micccy/scoreboard/pcb/mic5677_displaydriver/front.pdf

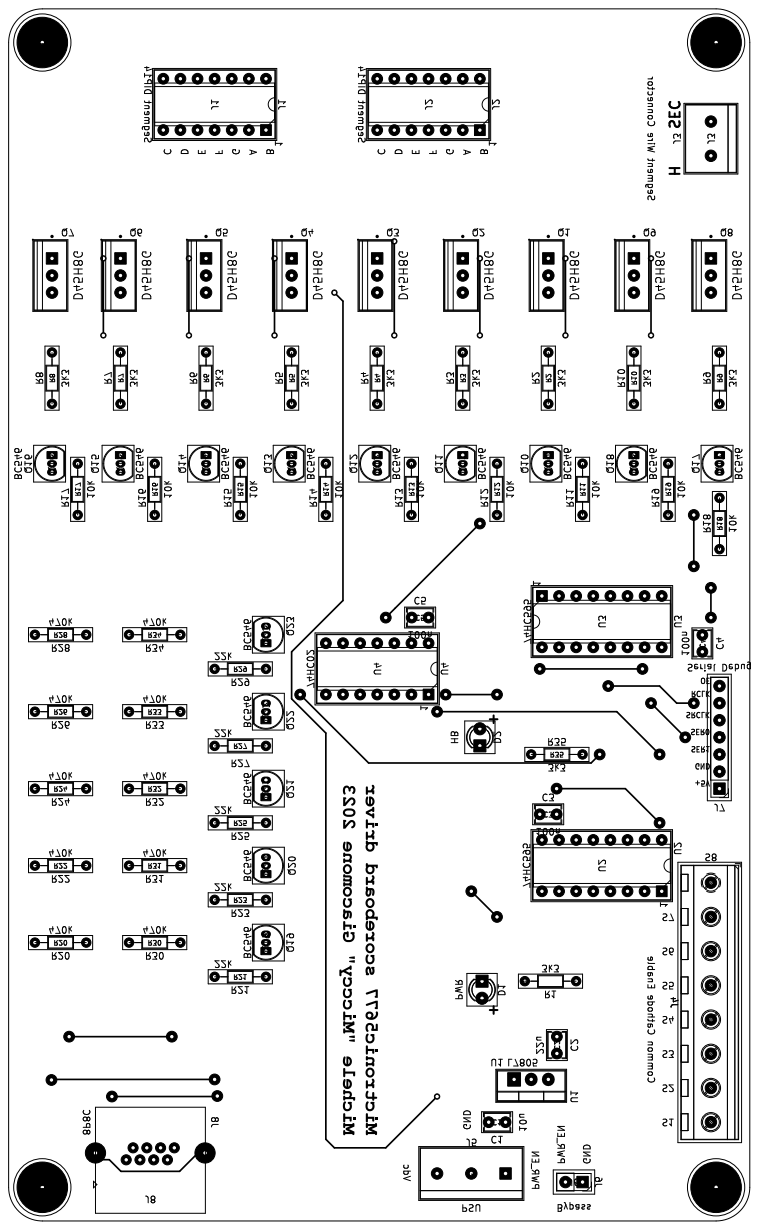
[picture p5: page 1]

H +5V GND + S6 GND B S5 GF SEC

Michele "Micccy" Giacomone 2023 S4S2 E SRCLK SER1 C OE 1 1 CEFDG 1 S8 S1S3 A SER0 GND S7 PWR_EN 1 PWR_EN RCLK DA + B 1 Q11
