micccy/scoreboard/pcb/mic5677_displaydriver/back.pdf

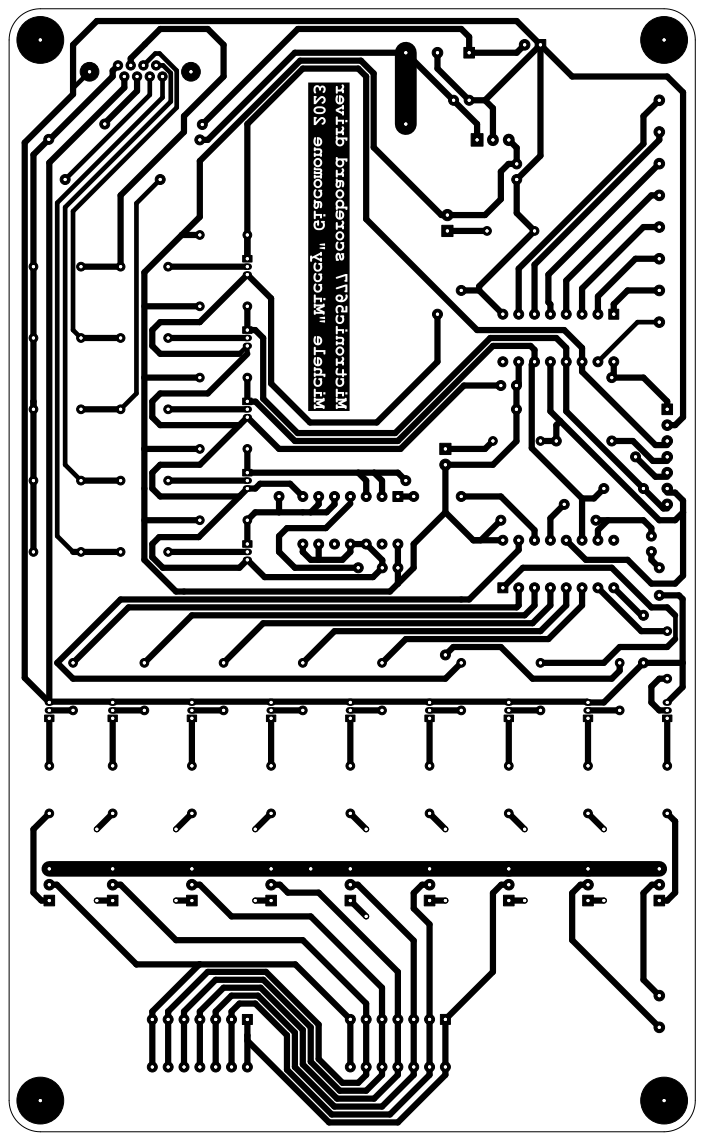
[picture p7: page 1]
